hojte/Bachelor2021/Arduino/Samples/tutorial_sample_code/tutorial_sample_code.ino

/*     Simple Stepper Motor Control Exaple Code
 *      
 *  by Dejan Nedelkovski, www.HowToMechatronics.com
 *  altered by Mathias Olsen
 */
// defines pins numbers
const int stepPin = 0; 
const int dirPin = 2; 
 
void setup() {
  // Sets the two pins as Outputs
  pinMode(stepPin,OUTPUT); 
  pinMode(dirPin,OUTPUT);
  Serial.begin(115200);
  delay(10); //Vent, elers går det for hurtigt
}
void loop() {
  pinMode(LED_BUILTIN, OUTPUT); 
  digitalWrite(LED_BUILTIN, 0);
  Serial.println("Counter-Clockwise");
  digitalWrite(dirPin,HIGH); // Enables the motor to move in a particular direction
  // Makes 200 pulses for making one full cycle rotation
  for(int x = 0; x < 1050; x++) {
    digitalWrite(stepPin,HIGH); 
    delayMicroseconds(500); 
    digitalWrite(stepPin,LOW); 
    delayMicroseconds(500); 
  }
  delay(1000); // One second delay

  pinMode(LED_BUILTIN, OUTPUT); 
  digitalWrite(LED_BUILTIN, 1);
  Serial.println("Clockwise");
  digitalWrite(dirPin,LOW); //Changes the rotations direction
  // Makes 400 pulses for making two full cycle rotation
  for(int x = 0; x < 1050; x++) {
    digitalWrite(stepPin,HIGH);
    delayMicroseconds(500);
    digitalWrite(stepPin,LOW);
    delayMicroseconds(500);
  }
  delay(1000);
}
